akornsys-rdi/ghostly-light/img/ghostly-light-2.png

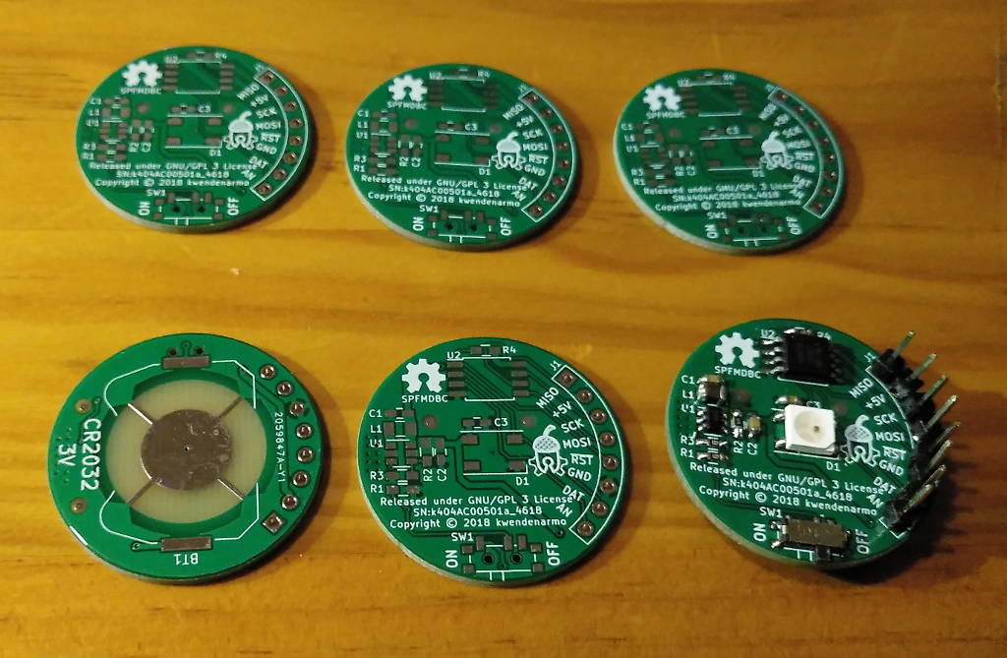
img/ghostly-light-2.png
