akornsys-rdi/ghostly-light/img/ghostly-light-4.png

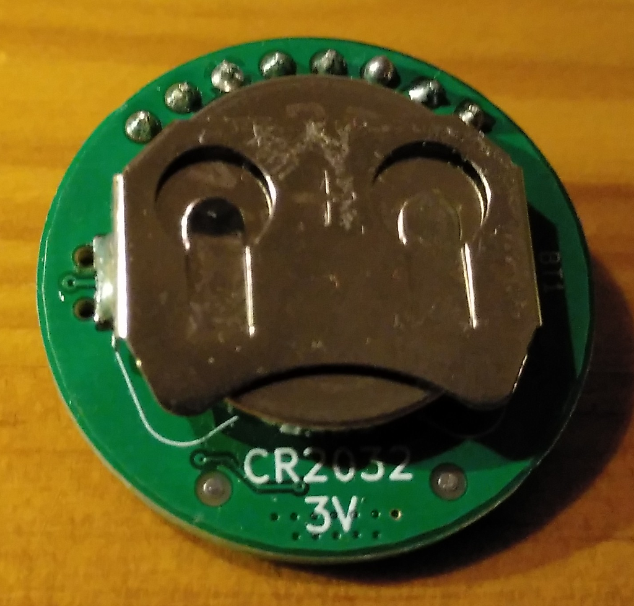
img/ghostly-light-4.png
