akornsys-rdi/ghostly-light/img/ghostly-light-8.png

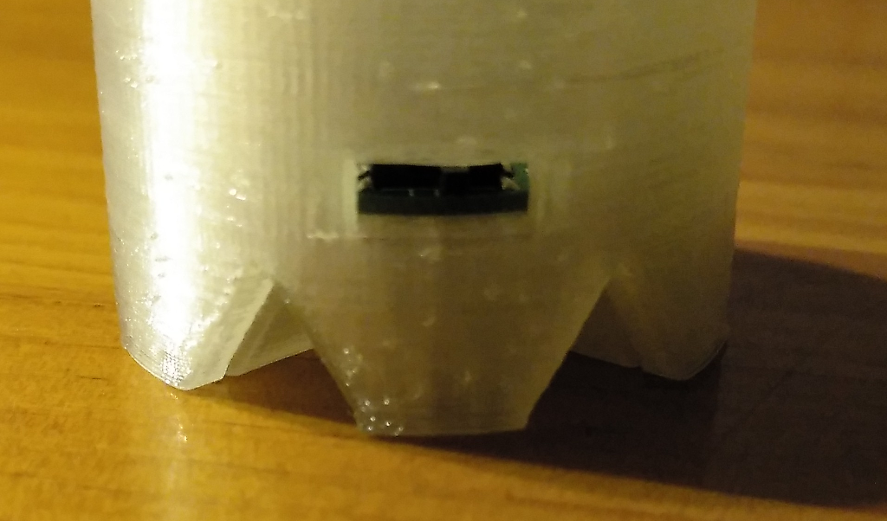
img/ghostly-light-8.png
