akornsys-rdi/ghostly-light/img/ghostly-light-10.png

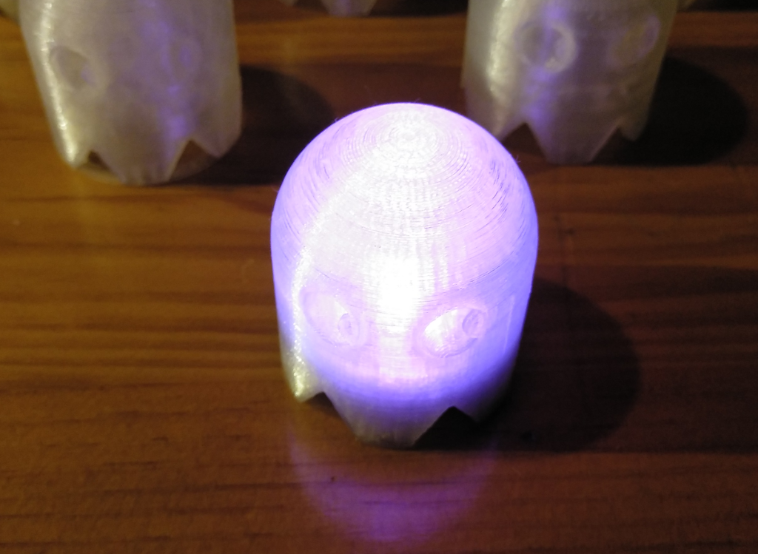
img/ghostly-light-10.png
