akornsys-rdi/ghostly-light/img/ghostly-light-13.png

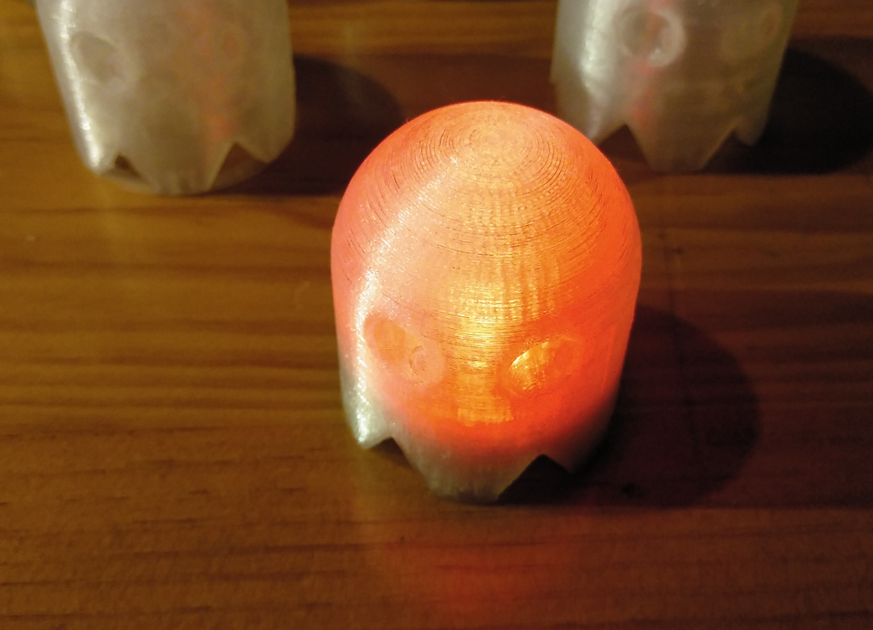
img/ghostly-light-13.png
